euvalennn/rpboard-squared/pcb/silkscreen/hack-club-2025-outline.png

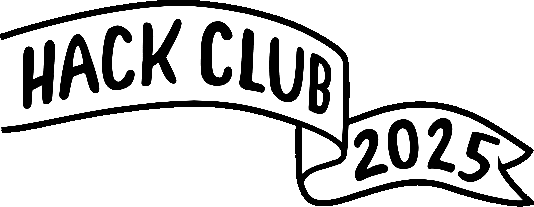
pcb/silkscreen/hack-club-2025-outline.png
