euvalennn/rpboard-squared/pcb/silkscreen/heidi-highway-car-outline.png

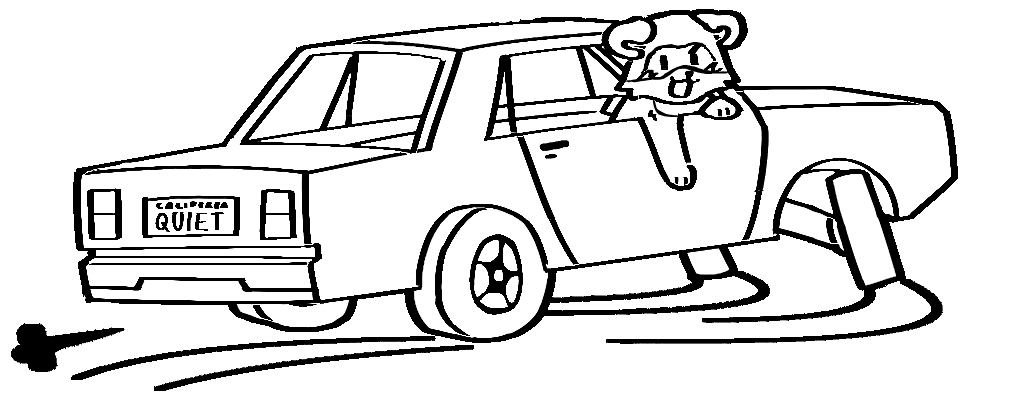
pcb/silkscreen/heidi-highway-car-outline.png
