euvalennn/rpboard-squared/pcb/silkscreen/orpheus-flag-outline-downscaled.png

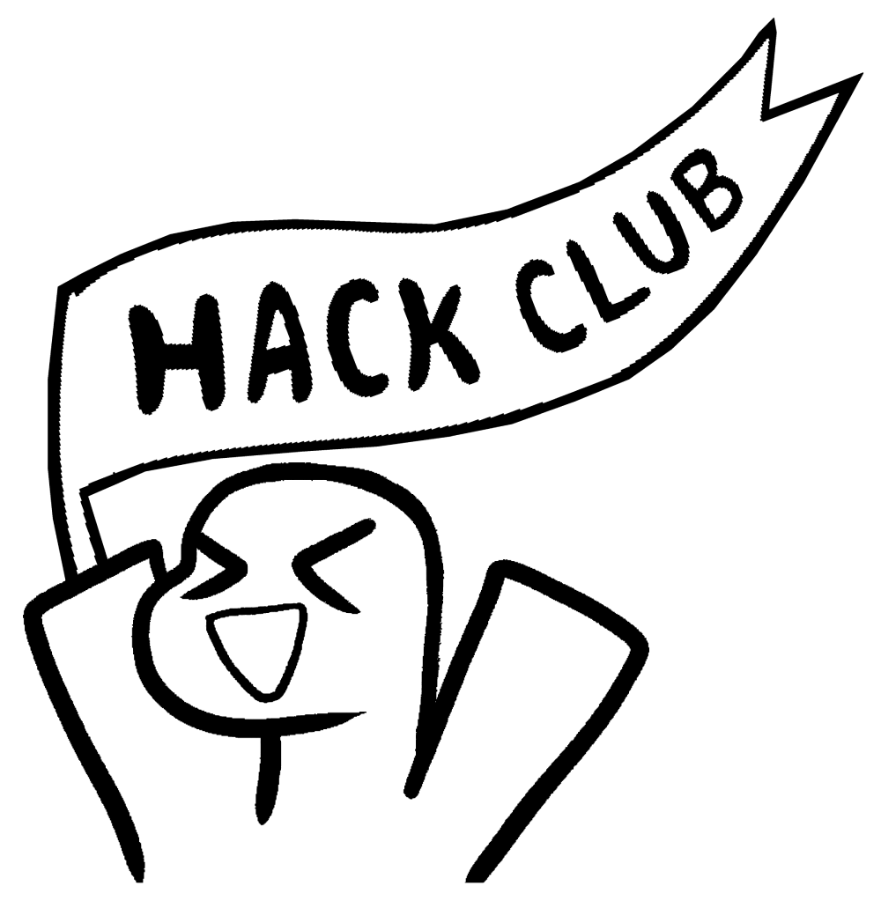
pcb/silkscreen/orpheus-flag-outline-downscaled.png
