euvalennn/rpboard-squared/pcb/silkscreen/orpheus-pf-outline.png

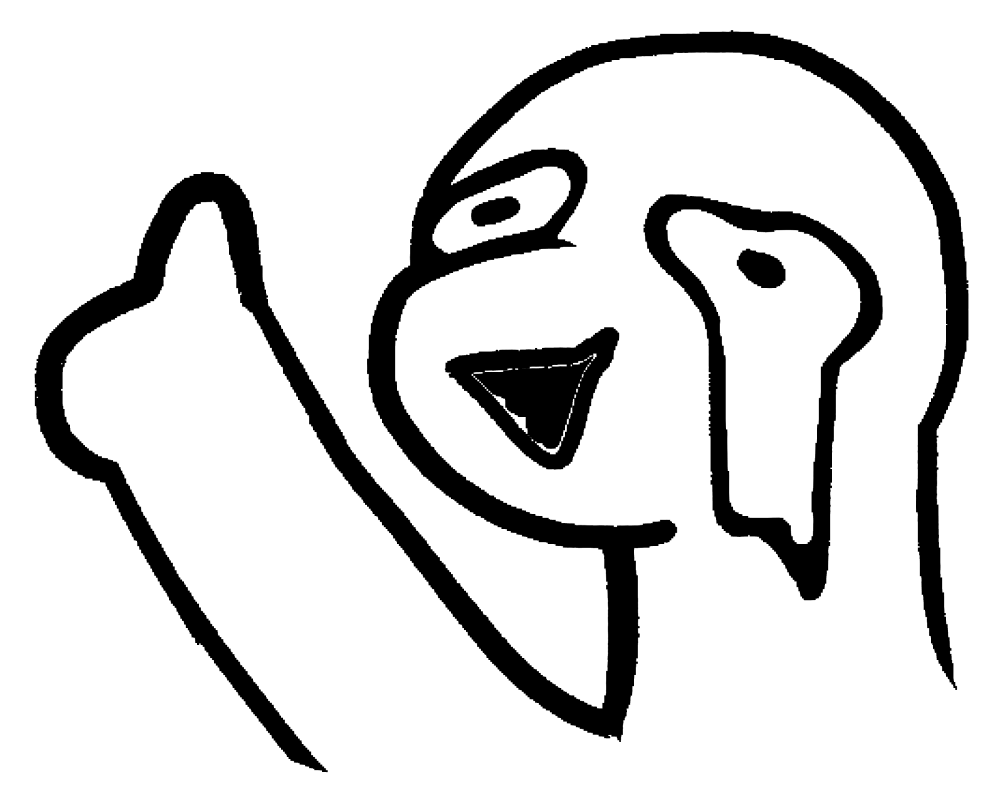
pcb/silkscreen/orpheus-pf-outline.png
